MateMch-iliauni/bachelor-s-thesis/final-website/assets/comp-esp32.jpg

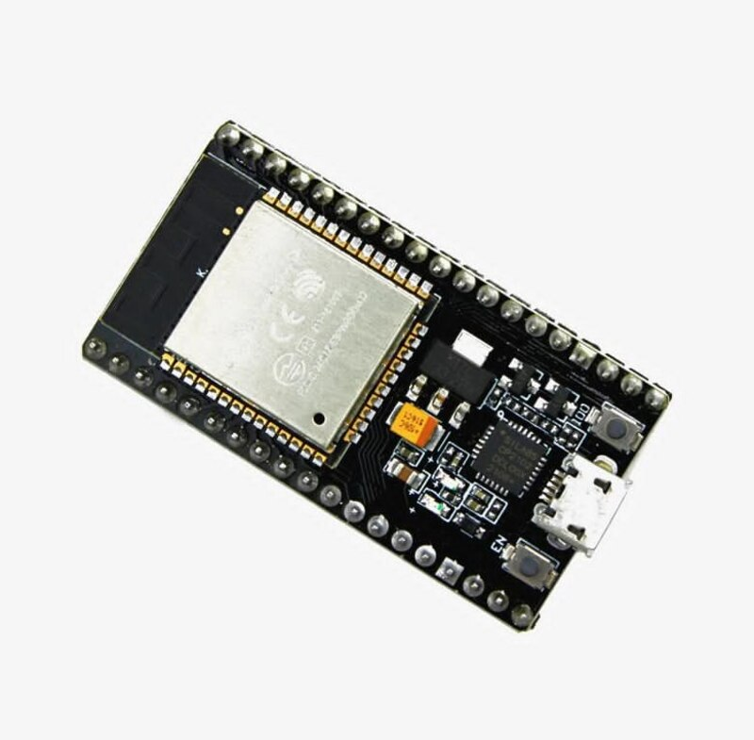
final-website/assets/comp-esp32.jpg
