MateMch-iliauni/bachelor-s-thesis/Production_drawings/cover_3Dmodel.png

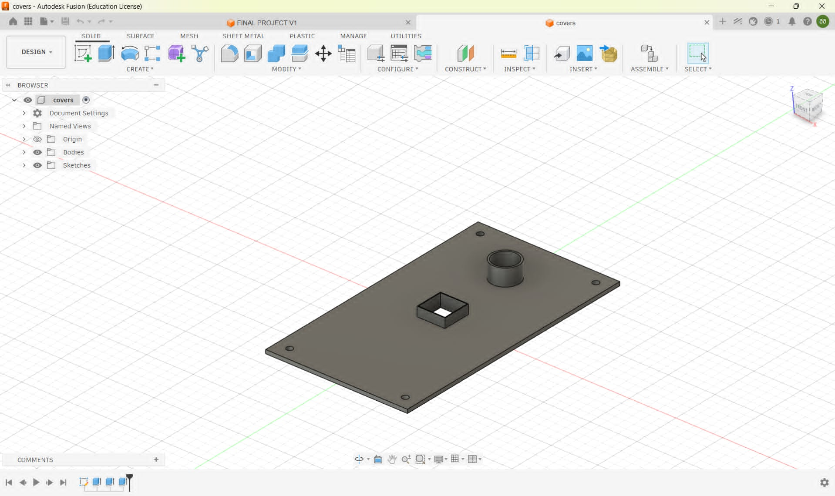
Production_drawings/cover_3Dmodel.png
