MateMch-iliauni/bachelor-s-thesis/project-diagrams/ელექტრული წრედი.png

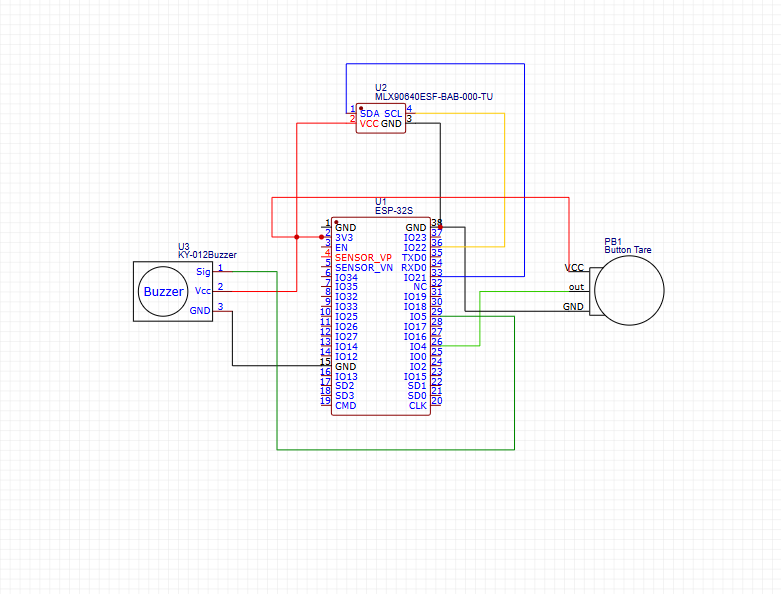
project-diagrams/ელექტრული წრედი.png
