MateMch-iliauni/bachelor-s-thesis/project-diagrams/მონტაჟის სქემა.png

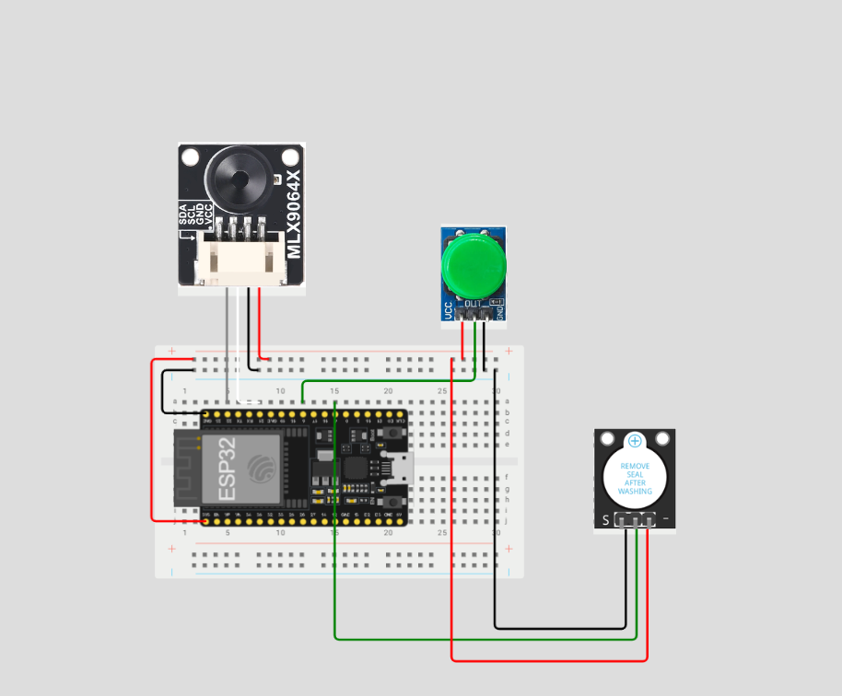
project-diagrams/მონტაჟის სქემა.png
